Ramis84/the-silent-night-customizable-cpap-muffler/images/v1-top-large.jpg

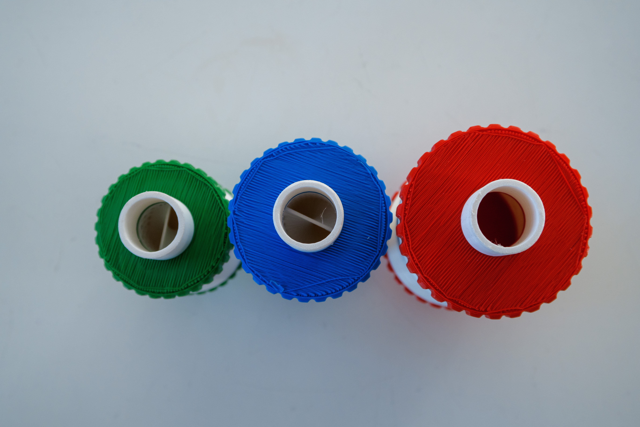
images/v1-top-large.jpg
