Ramis84/the-silent-night-customizable-cpap-muffler/v1-openscad/v1-large-endcap-male.stl

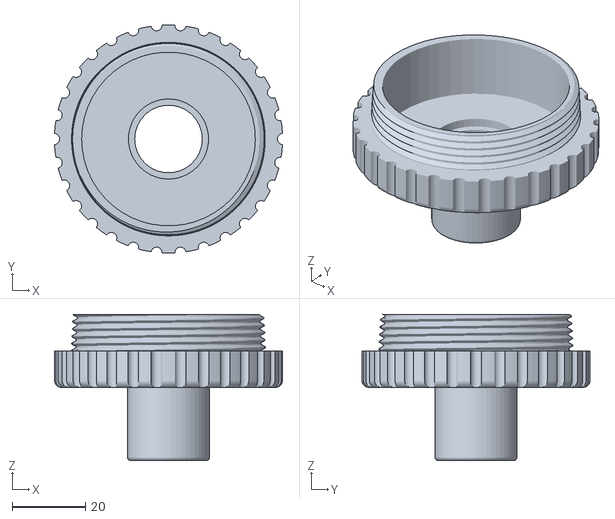
[picture p18: CAD file, 2026-02-11]
v1-openscad/v1-large-endcap-male.stl
62.4 x 62.5 x 40.0
