Ramis84/the-silent-night-customizable-cpap-muffler/v2-build123d/v2-end-cap-female-medium-2-5-extra-spacing.step

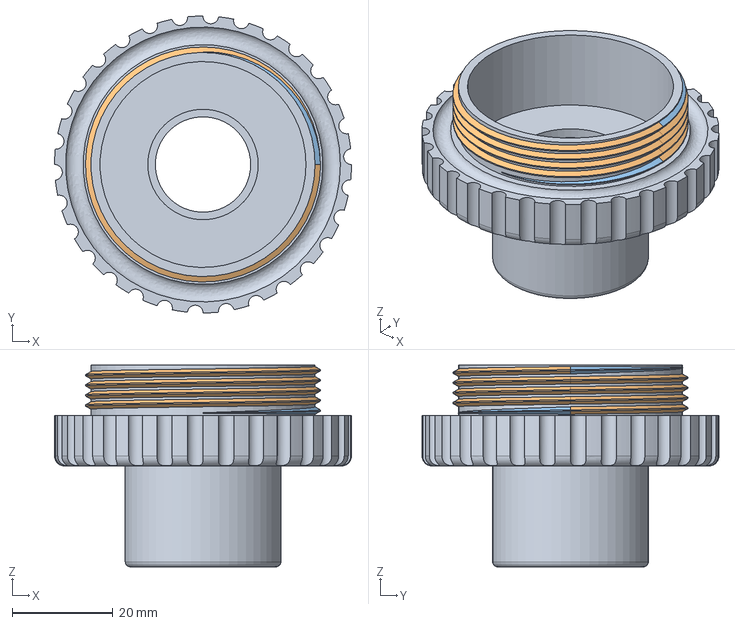
[picture p19: CAD file, 2026-02-17]
v2-build123d/v2-end-cap-female-medium-2-5-extra-spacing.step
58.9 x 58.9 x 40.0 mm
