Ramis84/the-silent-night-customizable-cpap-muffler/v1-openscad/v1-medium-body-with-edge.stl

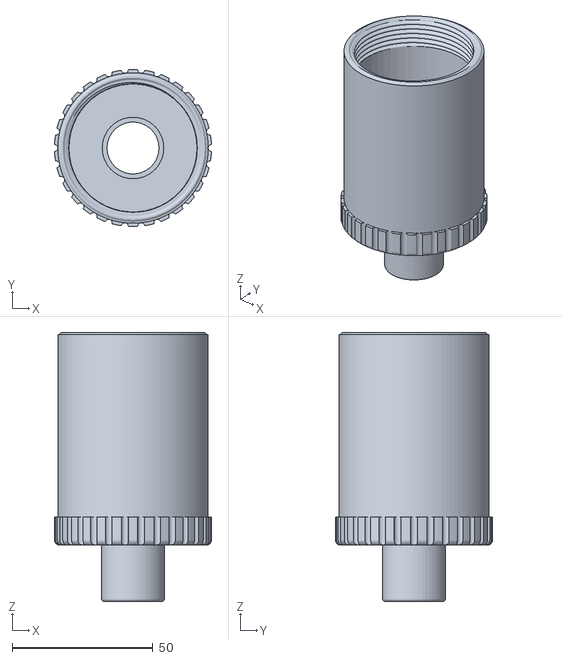
[picture p20: CAD file, 2026-02-11]
v1-openscad/v1-medium-body-with-edge.stl
55.9 x 56.0 x 95.7
