Ramis84/the-silent-night-customizable-cpap-muffler/v1-openscad/v1-small-body.stl

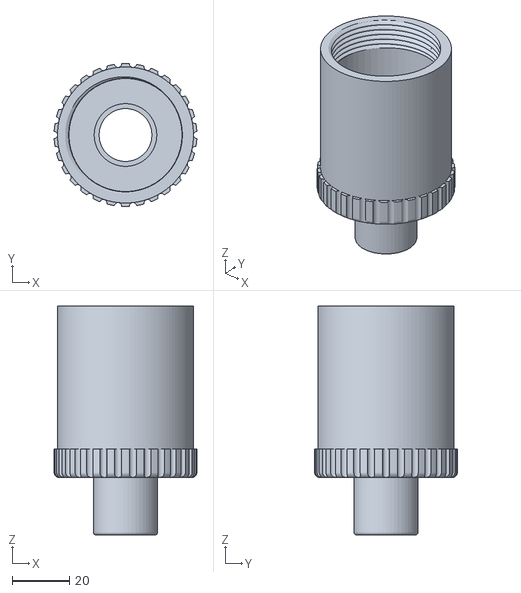
[picture p21: CAD file, 2026-02-11]
v1-openscad/v1-small-body.stl
49.9 x 50.0 x 80.0
