Ramis84/the-silent-night-customizable-cpap-muffler/v2-build123d/v2-end-cap-female-small-2-0.step

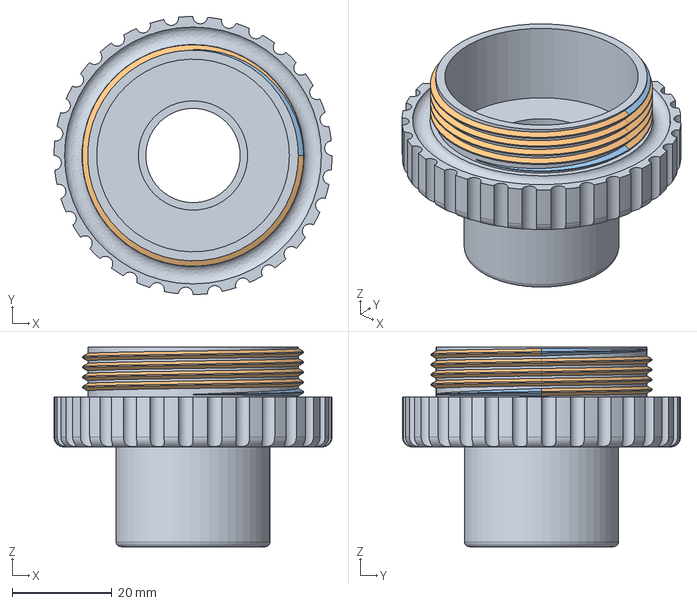
[picture p22: CAD file, 2026-02-17]
v2-build123d/v2-end-cap-female-small-2-0.step
55.7 x 55.7 x 40.0 mm
