Ramis84/the-silent-night-customizable-cpap-muffler/v2-build123d/v2-end-cap-female-large-2-5-extra-spacing.step

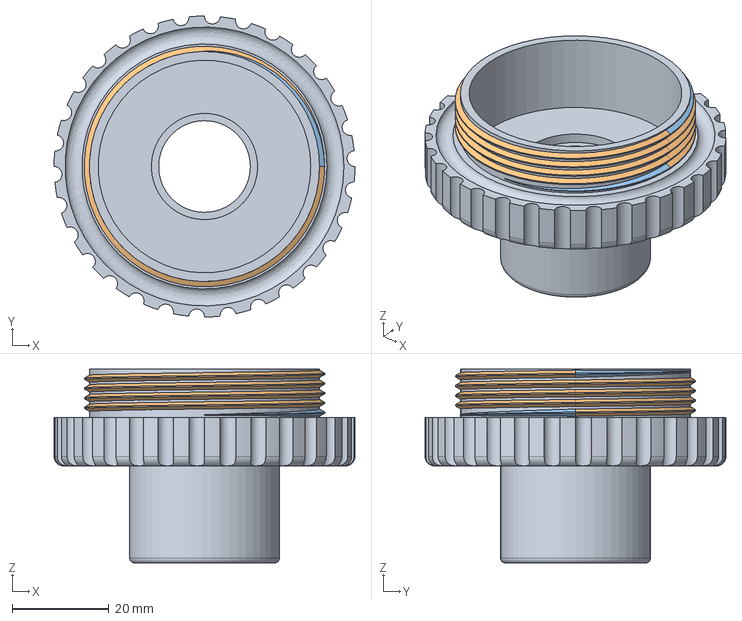
[picture p23: CAD file, 2026-02-17]
v2-build123d/v2-end-cap-female-large-2-5-extra-spacing.step
62.1 x 62.1 x 40.0 mm
