Ramis84/the-silent-night-customizable-cpap-muffler/v2-build123d/v2-body-male-small-100.step

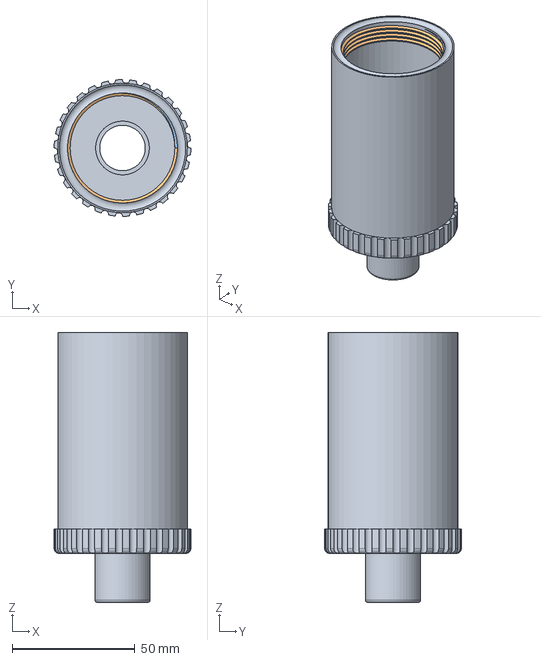
[picture p31: CAD file, 2026-02-17]
v2-build123d/v2-body-male-small-100.step
55.7 x 55.7 x 110.0 mm
