Ramis84/the-silent-night-customizable-cpap-muffler/v1-openscad/v1-small-innertube.stl

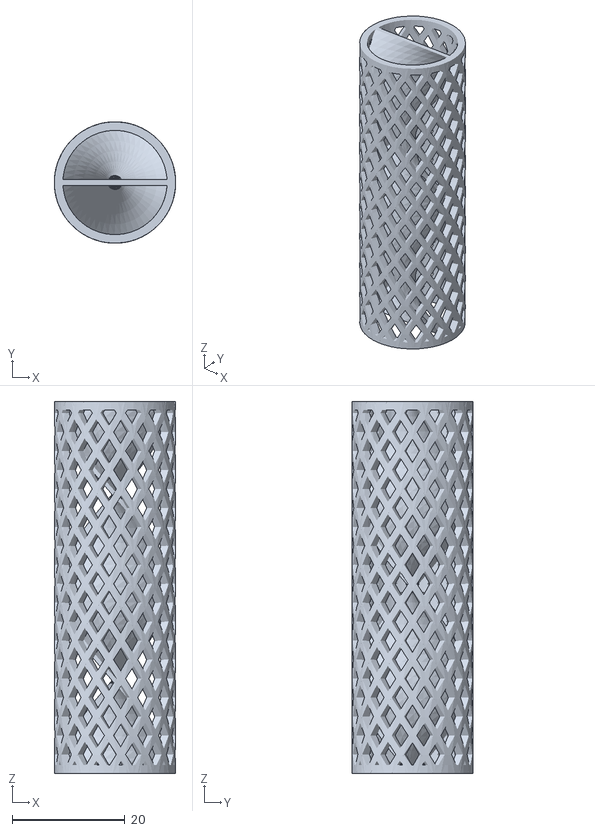
[picture p32: CAD file, 2026-02-11]
v1-openscad/v1-small-innertube.stl
21.6 x 21.6 x 66.0
