Ramis84/the-silent-night-customizable-cpap-muffler/v2-build123d/v2-body-male-small-120.step

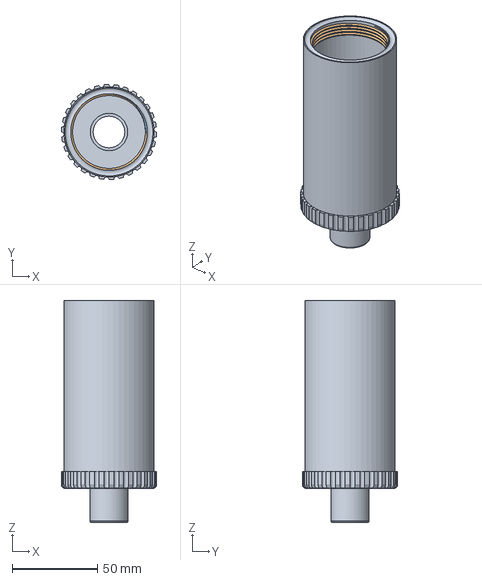
[picture p33: CAD file, 2026-02-17]
v2-build123d/v2-body-male-small-120.step
55.7 x 55.7 x 130.0 mm
