Ramis84/the-silent-night-customizable-cpap-muffler/v2-build123d/v2-inner-mesh-tube-120.step

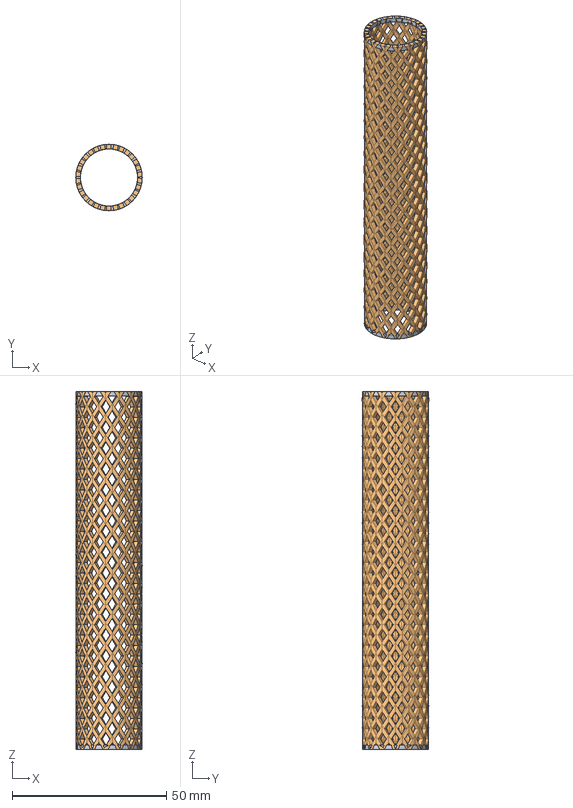
[picture p34: CAD file, 2026-02-17]
v2-build123d/v2-inner-mesh-tube-120.step
21.6 x 21.6 x 116.0 mm
