Ramis84/the-silent-night-customizable-cpap-muffler/v2-build123d/v2-body-male-large-120.step

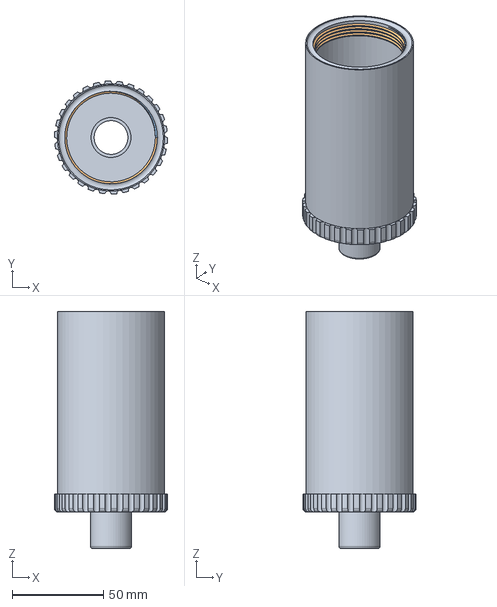
[picture p35: CAD file, 2026-02-17]
v2-build123d/v2-body-male-large-120.step
62.1 x 62.1 x 130.0 mm
