Ramis84/the-silent-night-customizable-cpap-muffler/v2-build123d/v2-body-male-small-70.step

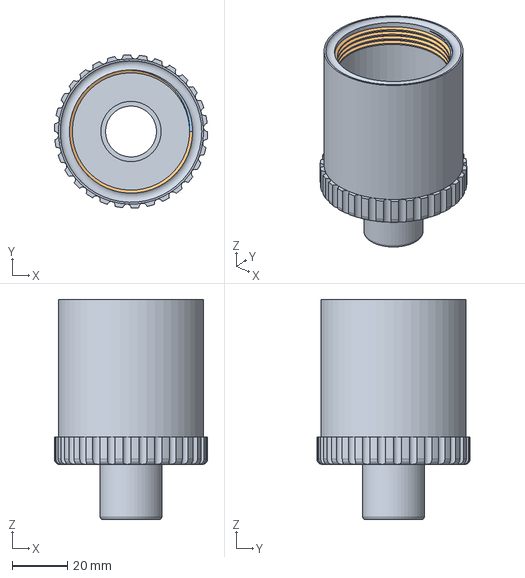
[picture p38: CAD file, 2026-02-17]
v2-build123d/v2-body-male-small-70.step
55.7 x 55.7 x 80.0 mm
