Ramis84/the-silent-night-customizable-cpap-muffler/v2-build123d/v2-body-male-medium-120.step

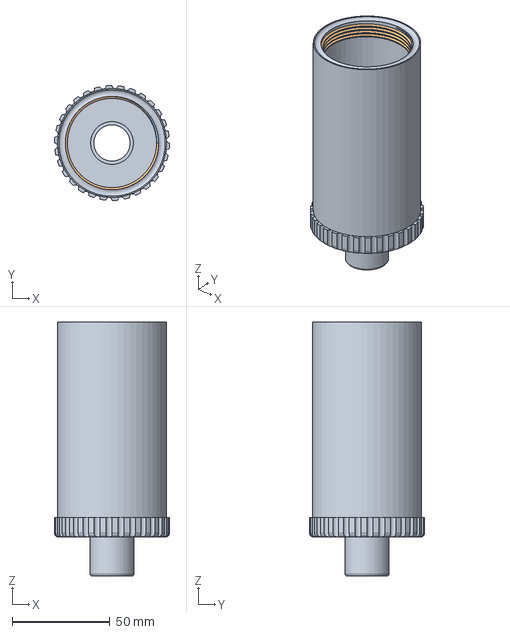
[picture p39: CAD file, 2026-02-17]
v2-build123d/v2-body-male-medium-120.step
58.9 x 58.9 x 130.0 mm
