Ramis84/the-silent-night-customizable-cpap-muffler/v2-build123d/v2-body-male-large-100.step

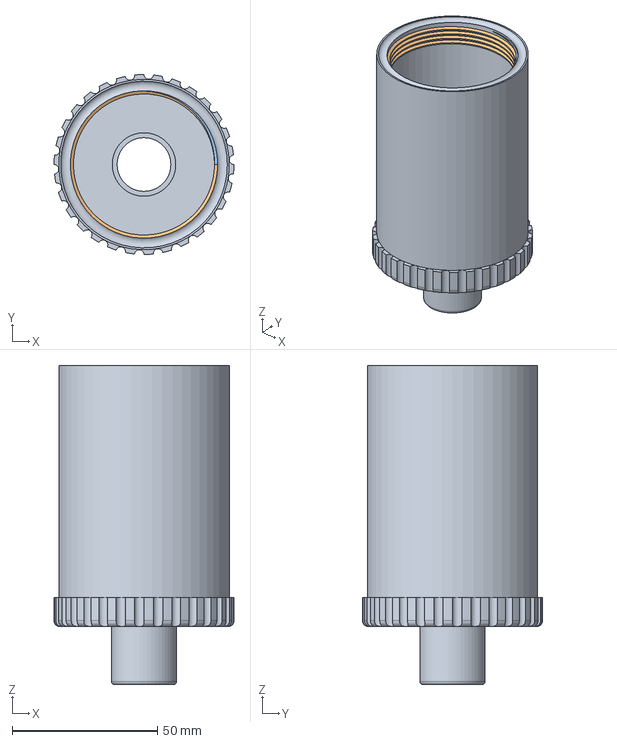
[picture p40: CAD file, 2026-02-17]
v2-build123d/v2-body-male-large-100.step
62.1 x 62.1 x 110.0 mm
